infrat/open-survey-system/firmware/receiver/include/oss_splash.h

#define splash_width 128
#define splash_height 64
static const unsigned char splashBitmap[] = {
    0x00, 0x00, 0x00, 0x00, 0x00, 0x00, 0x00, 0x00, 0x00, 0x00, 0x00, 0x00,
    0x00, 0x00, 0x00, 0x00, 0x00, 0x00, 0x00, 0x00, 0x00, 0x00, 0x00, 0x00,
    0x00, 0x00, 0x00, 0x00, 0x00, 0x00, 0x00, 0x00, 0x00, 0x00, 0x00, 0x00,
    0x00, 0x00, 0x00, 0x00, 0x00, 0x00, 0x00, 0x00, 0x00, 0x00, 0x00, 0x00,
    0x00, 0x00, 0x00, 0x00, 0x00, 0x00, 0x00, 0x00, 0x00, 0x00, 0x00, 0x00,
    0x00, 0x00, 0x00, 0x00, 0x00, 0x00, 0x00, 0x00, 0x07, 0x00, 0x00, 0x00,
    0x00, 0x00, 0x00, 0x00, 0x00, 0x00, 0x00, 0x00, 0x00, 0x00, 0x00, 0xc0,
    0x1f, 0x00, 0x00, 0x00, 0x00, 0x00, 0x00, 0x00, 0x00, 0x00, 0x00, 0x00,
    0x00, 0x00, 0x00, 0xf0, 0x7f, 0x00, 0x00, 0x00, 0x00, 0x00, 0x00, 0x00,
    0x00, 0x00, 0x00, 0x00, 0x00, 0x00, 0x00, 0xf8, 0xf8, 0x00, 0x00, 0x00,
    0x00, 0x00, 0x00, 0x00, 0x00, 0x00, 0x00, 0x00, 0x00, 0x00, 0x00, 0x3e,
    0xe0, 0x03, 0x00, 0x00, 0x00, 0x00, 0x00, 0x00, 0x00, 0x00, 0x00, 0x00,
    0x00, 0x00, 0x80, 0x0f, 0x80, 0x0f, 0x00, 0x00, 0x00, 0x00, 0x00, 0x00,
    0x00, 0x00, 0x00, 0x00, 0x00, 0x00, 0xe0, 0x03, 0x00, 0x3e, 0x00, 0x00,
    0x00, 0x00, 0x00, 0x00, 0x00, 0x00, 0x00, 0x00, 0x00, 0x00, 0xf0, 0x00,
    0x00, 0xf8, 0x00, 0x80, 0x07, 0x3e, 0xfc, 0x31, 0x18, 0x00, 0x00, 0x00,
    0x00, 0x00, 0x3c, 0x00, 0x00, 0xe0, 0x01, 0xe0, 0x0f, 0x7f, 0xfc, 0x31,
    0x18, 0x00, 0x00, 0x00, 0x00, 0x00, 0x1f, 0x80, 0x0f, 0x80, 0x07, 0x70,
    0x38, 0xe3, 0x0c, 0x70, 0x18, 0x00, 0x00, 0x00, 0x00, 0x80, 0x07, 0xc0,
    0x1f, 0x00, 0x1f, 0x30, 0x30, 0xc3, 0x0c, 0x70, 0x18, 0x00, 0x00, 0x00,
    0x00, 0xe0, 0x01, 0x60, 0x30, 0x00, 0x3c, 0x38, 0x70, 0xc3, 0x0c, 0xf0,
    0x18, 0x00, 0x00, 0x00, 0x00, 0x70, 0x00, 0x30, 0x60, 0x00, 0x38, 0x38,
    0x70, 0xc3, 0xfc, 0xf0, 0x19, 0x00, 0x00, 0x00, 0x00, 0x30, 0x00, 0x18,
    0xc0, 0x00, 0x70, 0x38, 0x70, 0x7f, 0xfc, 0xb0, 0x1b, 0x00, 0x00, 0x00,
    0x00, 0x30, 0x00, 0xc8, 0x98, 0x00, 0x60, 0x38, 0x70, 0x3f, 0x0c, 0x30,
    0x1f, 0x00, 0x00, 0x00, 0x00, 0x30, 0x00, 0xc8, 0x98, 0x00, 0x60, 0x30,
    0x30, 0x03, 0x0c, 0x30, 0x1e, 0x00, 0x00, 0x00, 0x00, 0x30, 0x00, 0x88,
    0x8d, 0x00, 0x60, 0x70, 0x18, 0x03, 0x0c, 0x30, 0x1c, 0x00, 0x00, 0x00,
    0x00, 0x30, 0x00, 0x18, 0xc7, 0x00, 0x60, 0xe0, 0x1f, 0x03, 0xfc, 0x31,
    0x18, 0x00, 0x00, 0x00, 0x00, 0x30, 0x00, 0x30, 0x62, 0x00, 0x60, 0x80,
    0x07, 0x03, 0xfc, 0x31, 0x18, 0x00, 0x00, 0x00, 0x00, 0x30, 0x00, 0x60,
    0x30, 0x00, 0x60, 0x00, 0x00, 0x00, 0x00, 0x00, 0x00, 0x00, 0x00, 0x00,
    0x00, 0x30, 0x00, 0xc0, 0x1f, 0x00, 0x60, 0x00, 0x00, 0x00, 0x00, 0x00,
    0x00, 0x00, 0x00, 0x00, 0x00, 0x30, 0x00, 0x80, 0x0f, 0x00, 0x60, 0x00,
    0x00, 0x00, 0x00, 0x00, 0x00, 0x00, 0x00, 0x00, 0x00, 0x30, 0x00, 0x00,
    0x00, 0x00, 0x60, 0xc0, 0x61, 0x18, 0x1f, 0x83, 0xf9, 0x19, 0x06, 0x00,
    0x00, 0x30, 0x00, 0x00, 0x00, 0x00, 0x60, 0xe0, 0x63, 0x98, 0x3f, 0x83,
    0xf9, 0x19, 0x06, 0x00, 0x00, 0x30, 0x00, 0x00, 0x00, 0x00, 0x60, 0x30,
    0x62, 0x98, 0x71, 0xc6, 0x18, 0x30, 0x03, 0x00, 0x00, 0x30, 0x00, 0xc0,
    0x1f, 0x00, 0x60, 0x30, 0x60, 0x98, 0x61, 0xc6, 0x18, 0x30, 0x03, 0x00,
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
